pdp7/memory-display/images/photo1.jpg

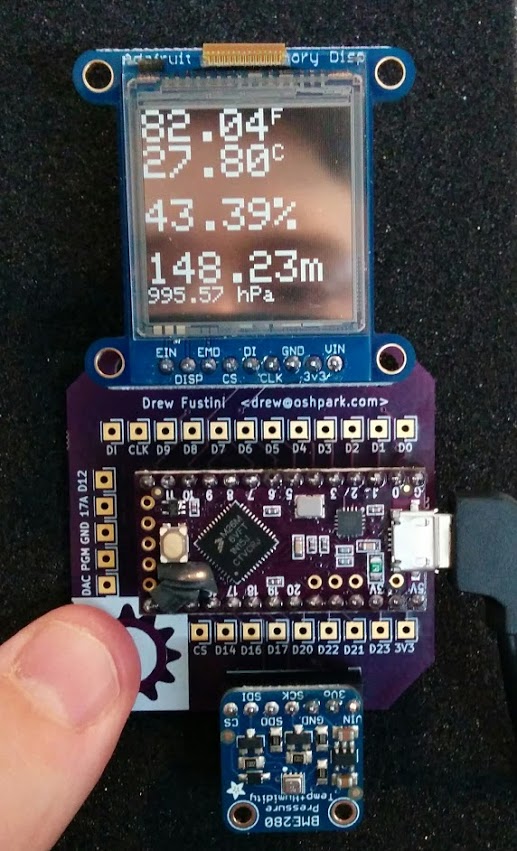
images/photo1.jpg
