pdp7/memory-display/images/photo2.jpg

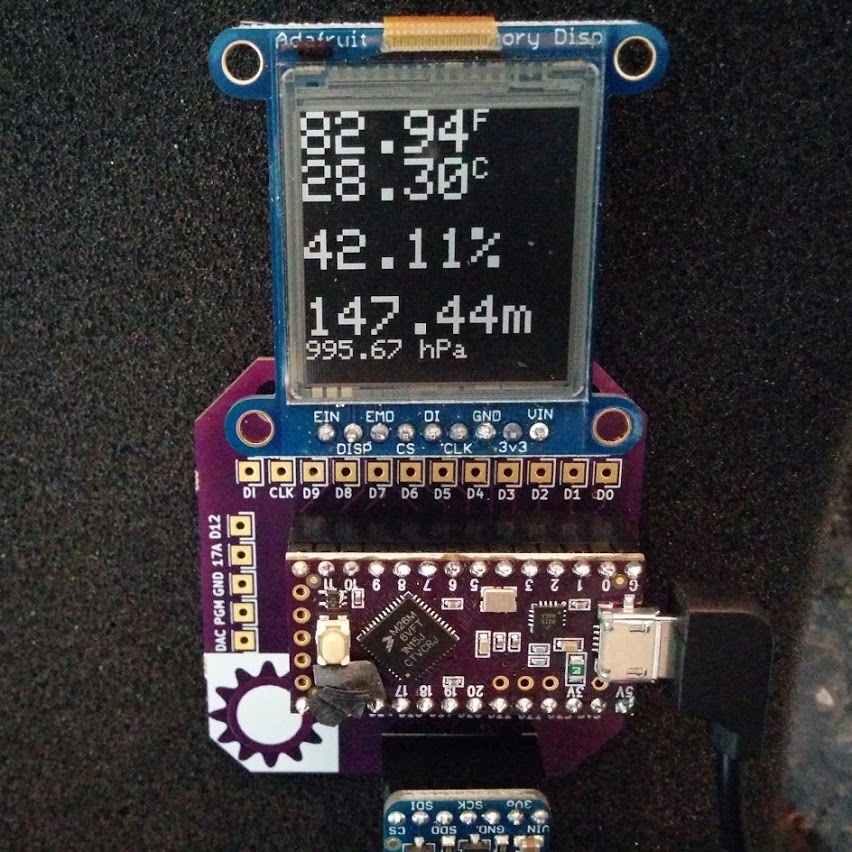
images/photo2.jpg
