pdp7/memory-display/images/photo3.jpg

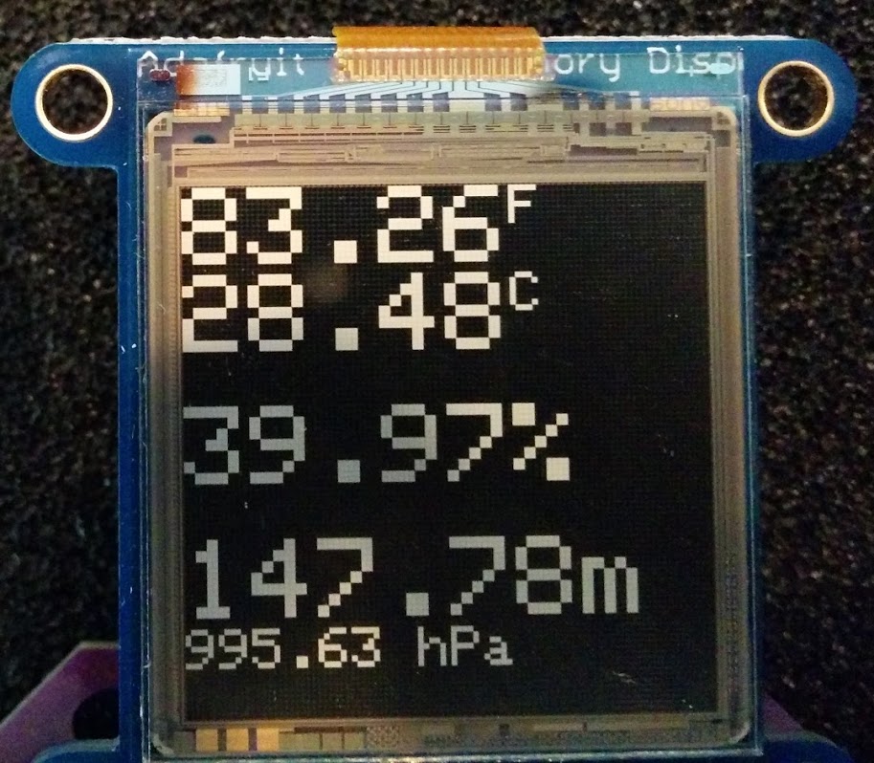
images/photo3.jpg
