pdp7/memory-display/images/photo4.jpg

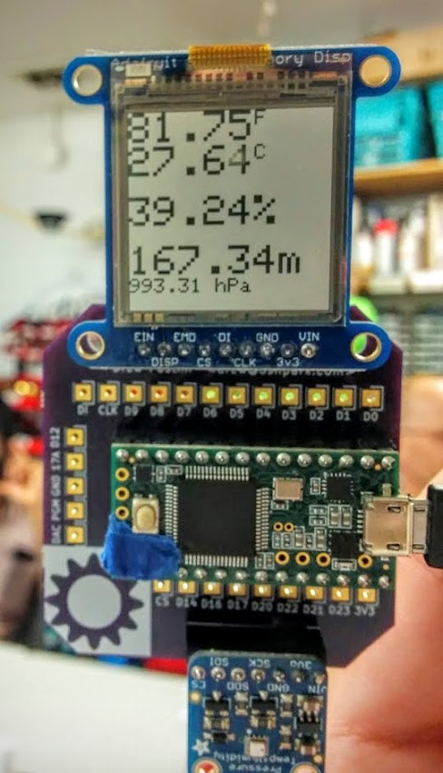
images/photo4.jpg
